AbdelrahmanSalemQotb/EGI_GraduationProject/Mechanical Files/3D/STEP files/Apollo BVM - Servo shim - 1mm.STEP

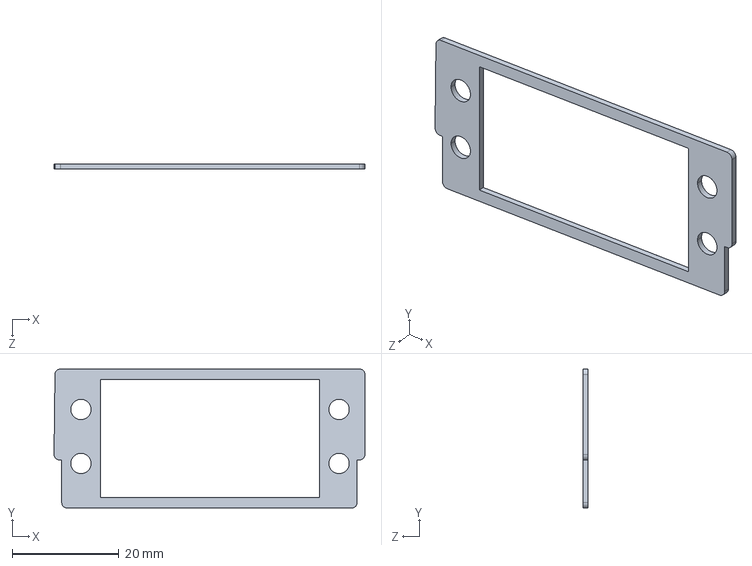
[picture p16: CAD file, 2022-06-29]
Mechanical Files/3D/STEP files/Apollo BVM - Servo shim - 1mm.STEP
58.2 x 26.0 x 1.00 mm
