AbdelrahmanSalemQotb/EGI_GraduationProject/Mechanical Files/3D/STEP files/Apollo BVM - BVM Support - Clamp Arm.STEP

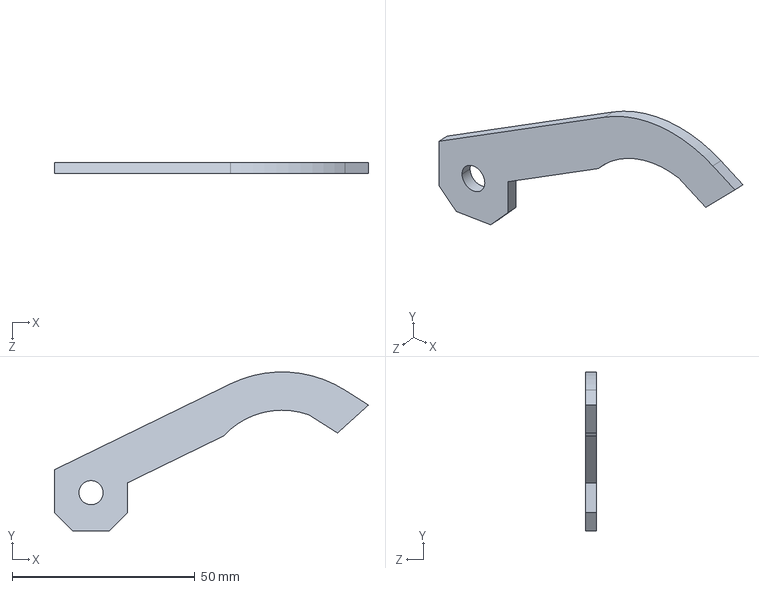
[picture p17: CAD file, 2022-06-29]
Mechanical Files/3D/STEP files/Apollo BVM - BVM Support - Clamp Arm.STEP
86.0 x 43.5 x 3.00 mm
