AbdelrahmanSalemQotb/EGI_GraduationProject/Mechanical Files/3D/STEP files/Apollo BVM - Linear Gear Housing Base.STEP

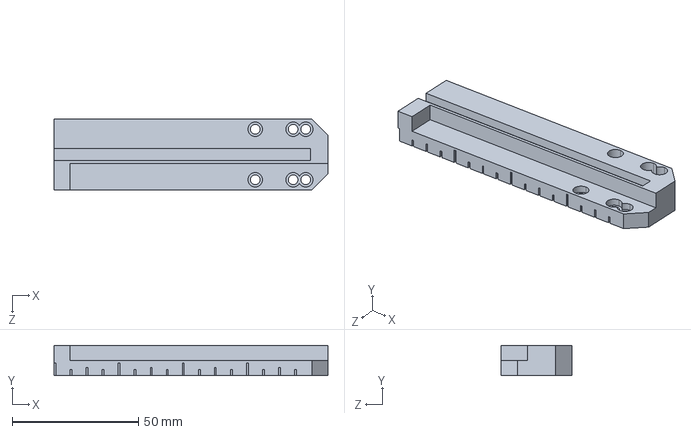
[picture p18: CAD file, 2022-06-29]
Mechanical Files/3D/STEP files/Apollo BVM - Linear Gear Housing Base.STEP
108.5 x 12.1 x 27.9 mm
